vamvictor/Centinela-Nerf/Aplicacion/diana.png

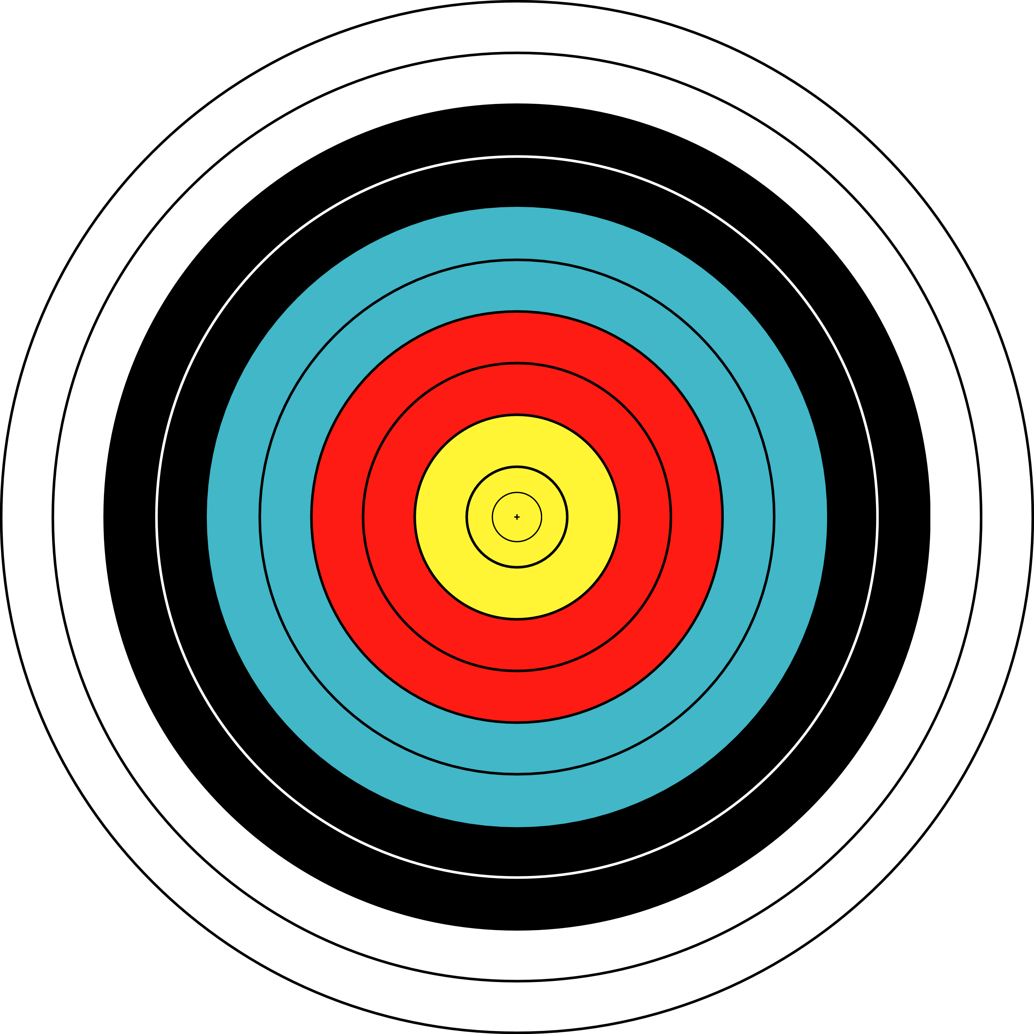
Aplicacion/diana.png
