vamvictor/Centinela-Nerf/Aplicacion/images/Bush/1.jpg

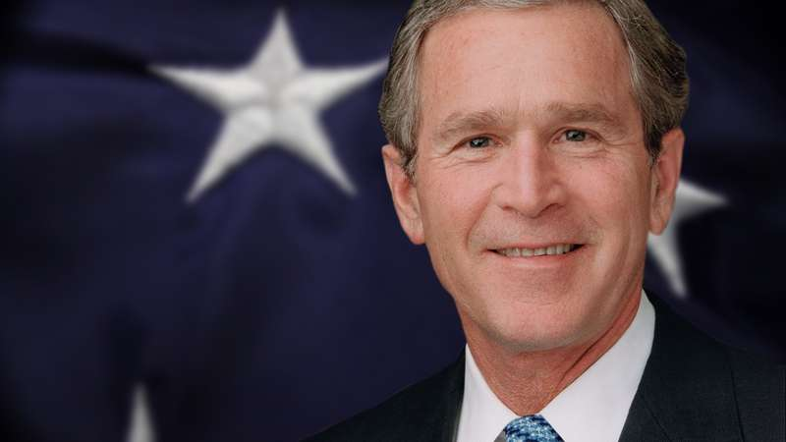
Aplicacion/images/Bush/1.jpg
