vamvictor/Centinela-Nerf/Aplicacion/images/Bush/2.jpg

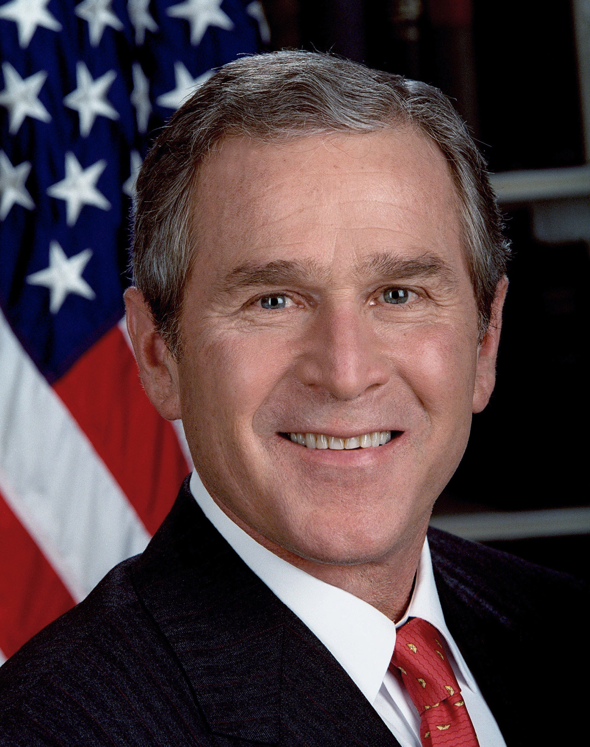
Aplicacion/images/Bush/2.jpg
