vamvictor/Centinela-Nerf/Aplicacion/images/Bush/3.jpg

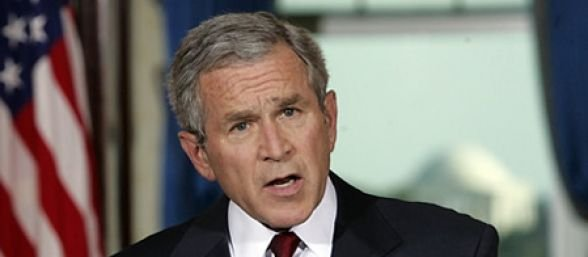
Aplicacion/images/Bush/3.jpg
