vamvictor/Centinela-Nerf/Aplicacion/images/Bush/4.jpg

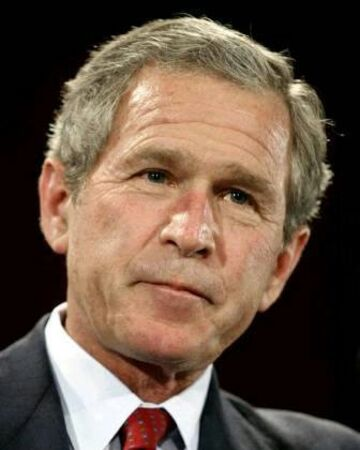
Aplicacion/images/Bush/4.jpg
