vamvictor/Centinela-Nerf/Aplicacion/images/Bush/5.jpg

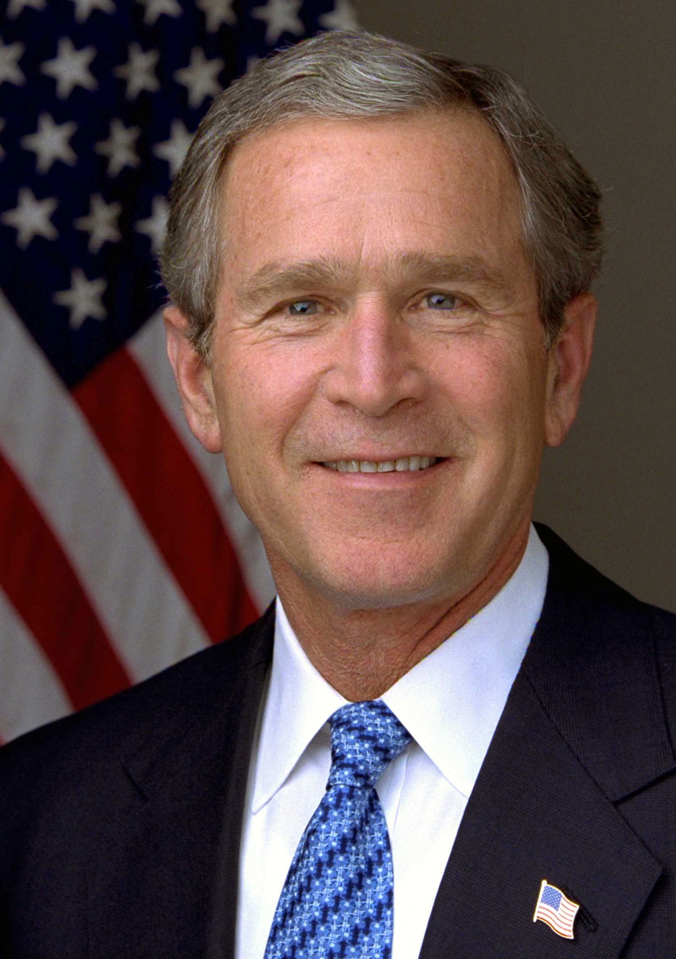
Aplicacion/images/Bush/5.jpg
