vamvictor/Centinela-Nerf/Aplicacion/images/Desconocidos/1.jpg

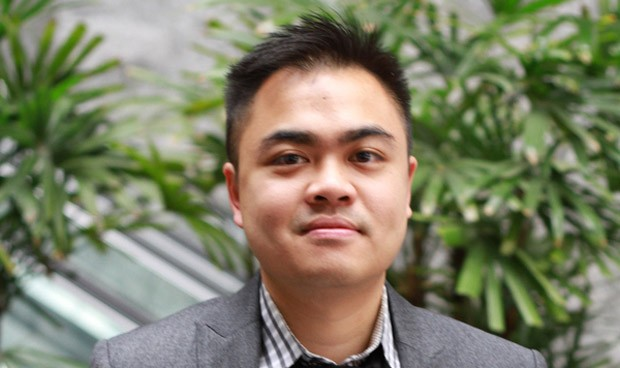
Aplicacion/images/Desconocidos/1.jpg
