vamvictor/Centinela-Nerf/Aplicacion/images/Desconocidos/2.png

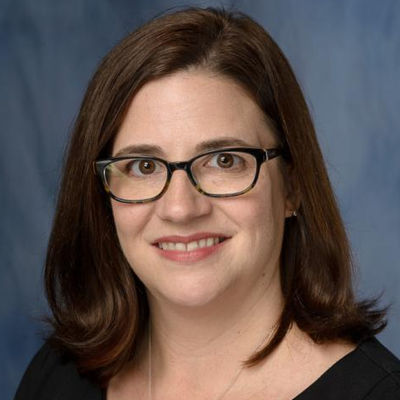
Aplicacion/images/Desconocidos/2.png
