vamvictor/Centinela-Nerf/Aplicacion/images/Desconocidos/3.jpg

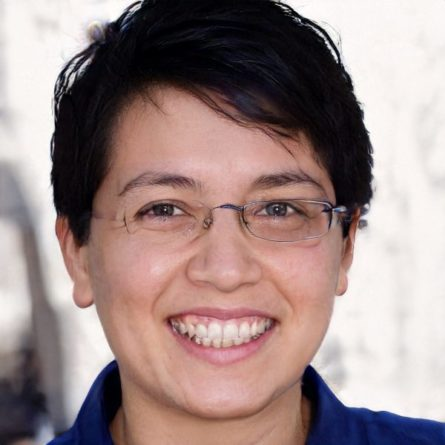
Aplicacion/images/Desconocidos/3.jpg
