vamvictor/Centinela-Nerf/Aplicacion/images/Desconocidos/4.jpg

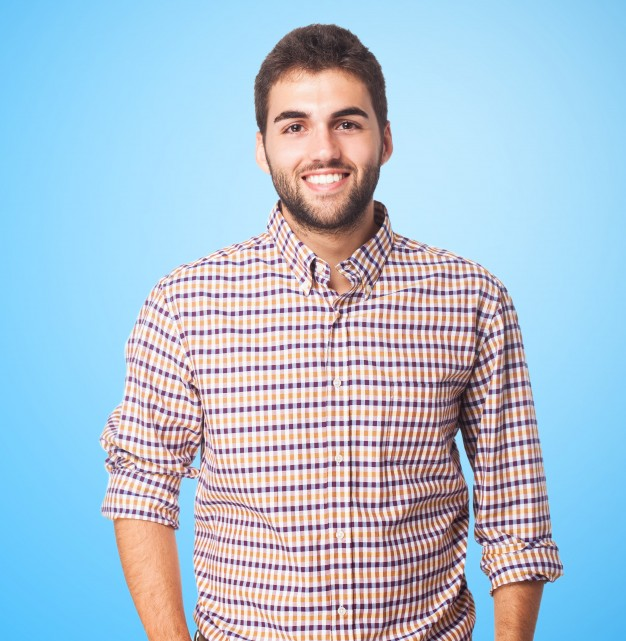
Aplicacion/images/Desconocidos/4.jpg
