vamvictor/Centinela-Nerf/Aplicacion/images/Desconocidos/5.jpg

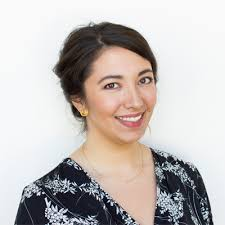
Aplicacion/images/Desconocidos/5.jpg
