vamvictor/Centinela-Nerf/Aplicacion/images/Desconocidos/6.jpg

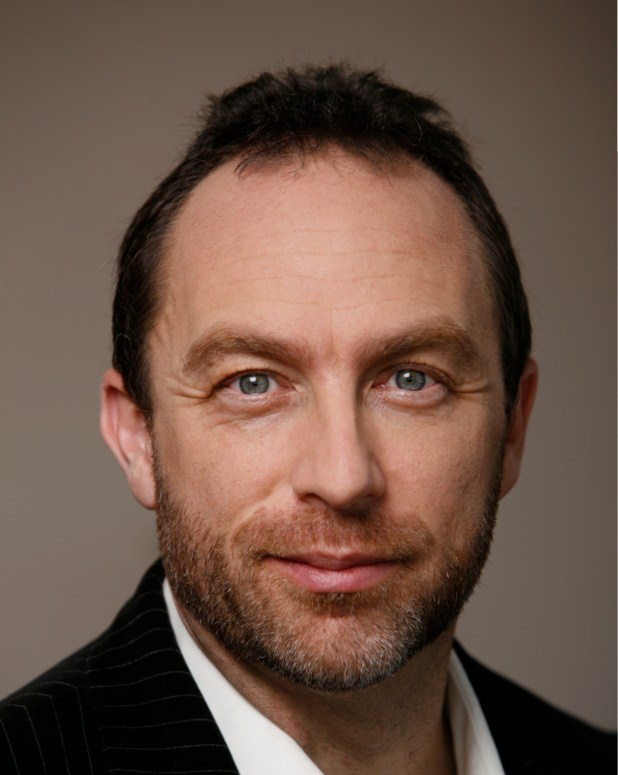
Aplicacion/images/Desconocidos/6.jpg
