vamvictor/Centinela-Nerf/Aplicacion/images/Desconocidos/7.jpg

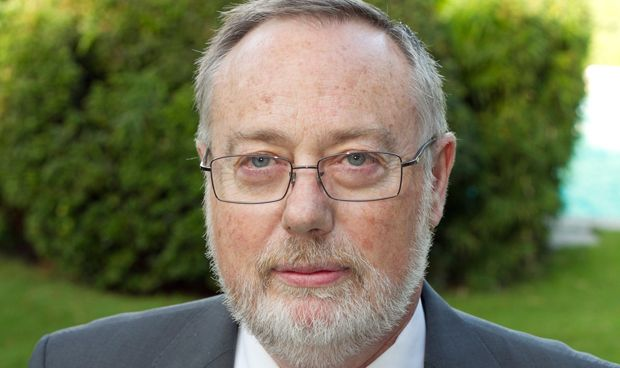
Aplicacion/images/Desconocidos/7.jpg
