vamvictor/Centinela-Nerf/Aplicacion/images/Desconocidos/8.jpg

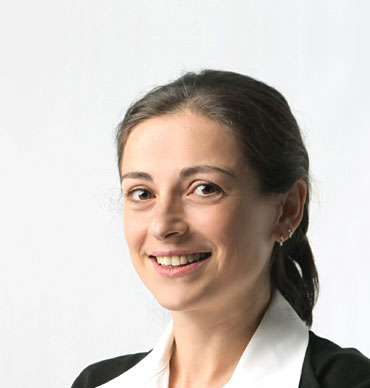
Aplicacion/images/Desconocidos/8.jpg
