vamvictor/Centinela-Nerf/Aplicacion/images/Kennedy/1.jpg

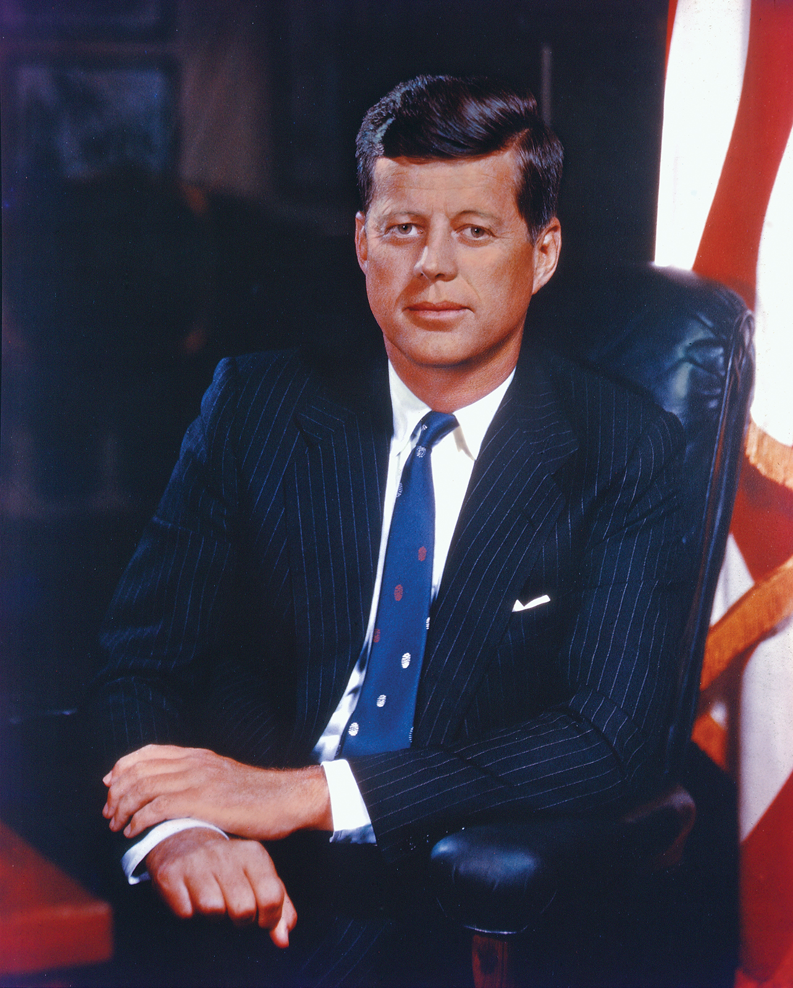
Aplicacion/images/Kennedy/1.jpg
