vamvictor/Centinela-Nerf/Aplicacion/images/Kennedy/2.jpg

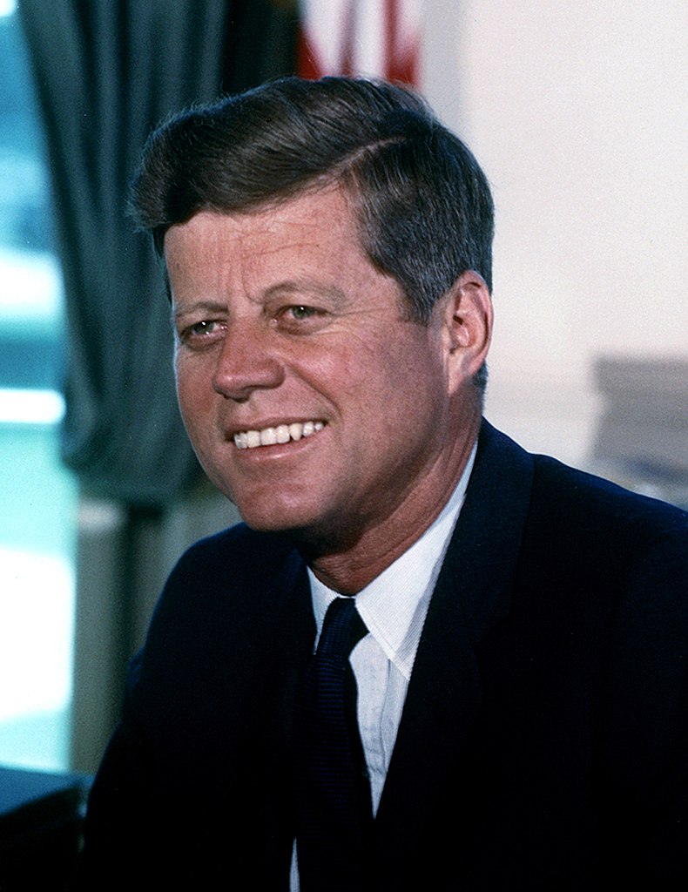
Aplicacion/images/Kennedy/2.jpg
