vamvictor/Centinela-Nerf/Aplicacion/images/Kennedy/3.jpg

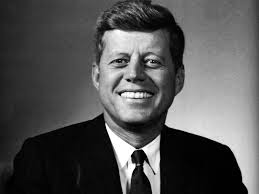
Aplicacion/images/Kennedy/3.jpg
