vamvictor/Centinela-Nerf/Aplicacion/images/Kennedy/4.jpg

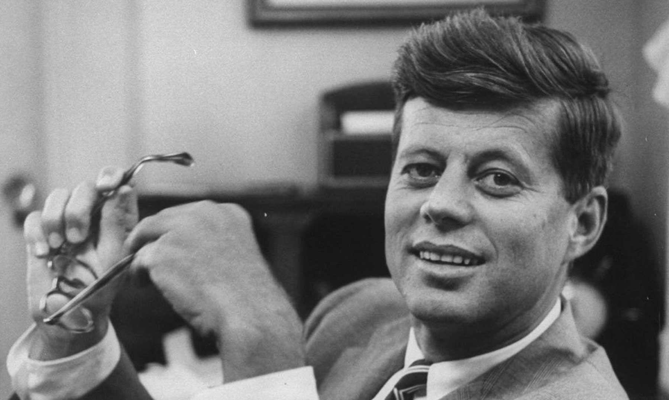
Aplicacion/images/Kennedy/4.jpg
