vamvictor/Centinela-Nerf/Aplicacion/images/Kennedy/5.jpg

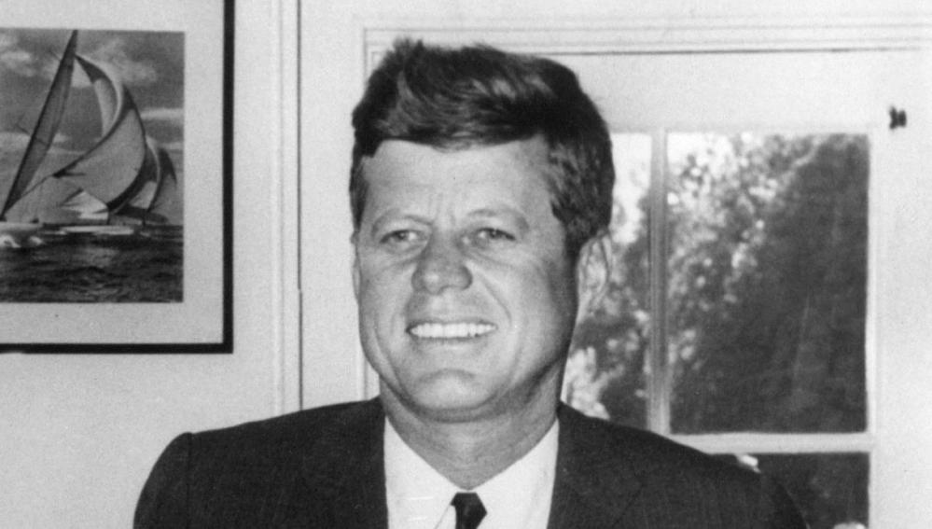
Aplicacion/images/Kennedy/5.jpg
