vamvictor/Centinela-Nerf/Aplicacion/images/Obama/1.jpg

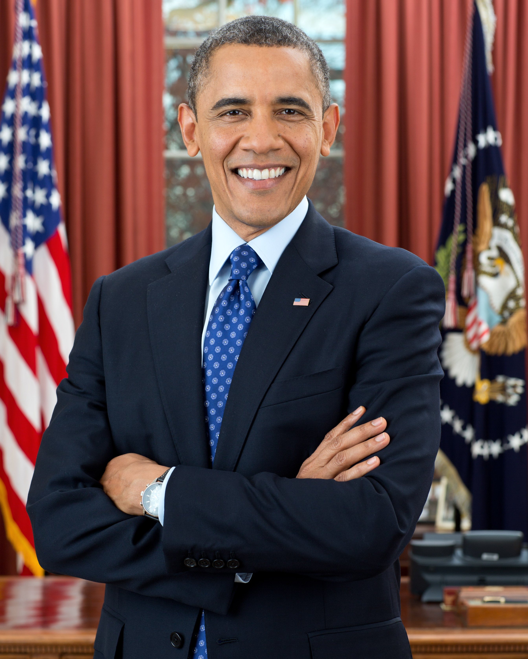
Aplicacion/images/Obama/1.jpg
