vamvictor/Centinela-Nerf/Aplicacion/images/Obama/2.jpg

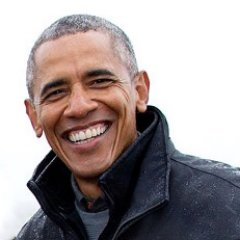
Aplicacion/images/Obama/2.jpg
