vamvictor/Centinela-Nerf/Aplicacion/images/Obama/3.jpg

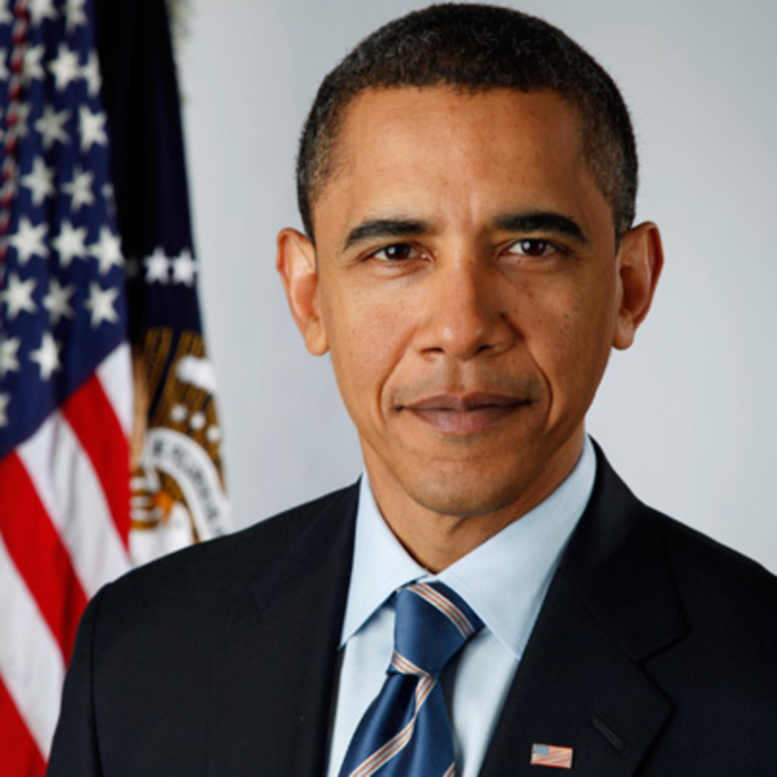
Aplicacion/images/Obama/3.jpg
