vamvictor/Centinela-Nerf/Aplicacion/images/Obama/4.jpg

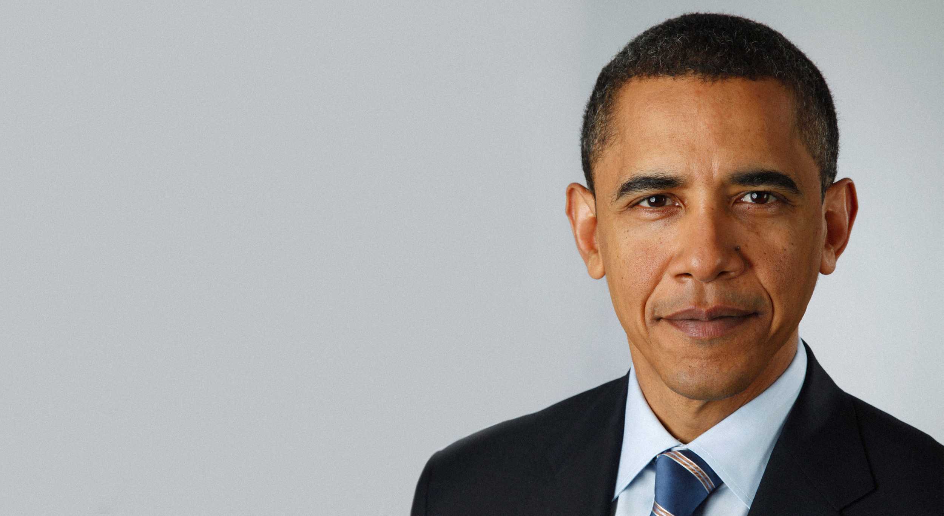
Aplicacion/images/Obama/4.jpg
