vamvictor/Centinela-Nerf/Aplicacion/images/Trump/1.jpg

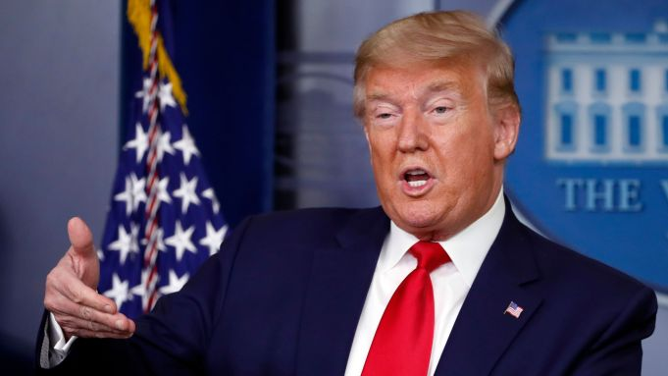
Aplicacion/images/Trump/1.jpg
