vamvictor/Centinela-Nerf/Aplicacion/images/Trump/2.jpg

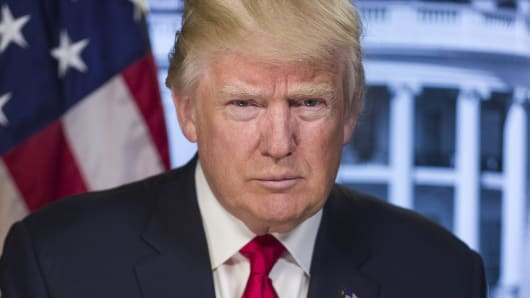
Aplicacion/images/Trump/2.jpg
