vamvictor/Centinela-Nerf/Aplicacion/images/Trump/3.jpg

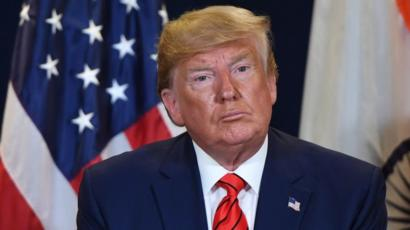
Aplicacion/images/Trump/3.jpg
