vamvictor/Centinela-Nerf/Aplicacion/images/Trump/5.jpg

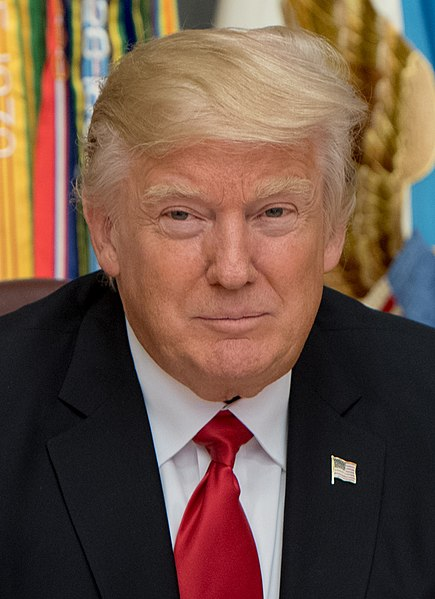
Aplicacion/images/Trump/5.jpg
