vamvictor/Centinela-Nerf/Aplicacion/images/Victor/1.jpg

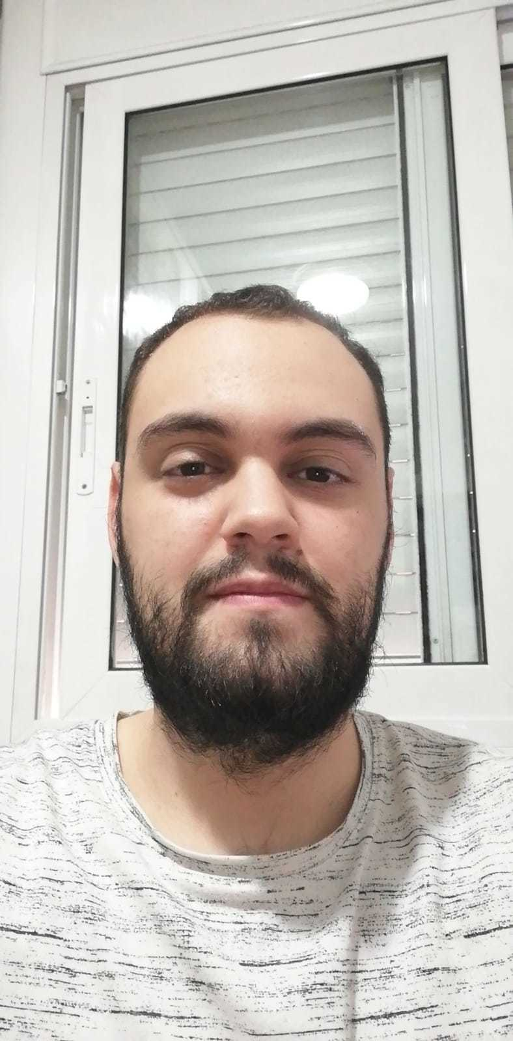
Aplicacion/images/Victor/1.jpg
