vamvictor/Centinela-Nerf/Aplicacion/images/Victor/2.jpg

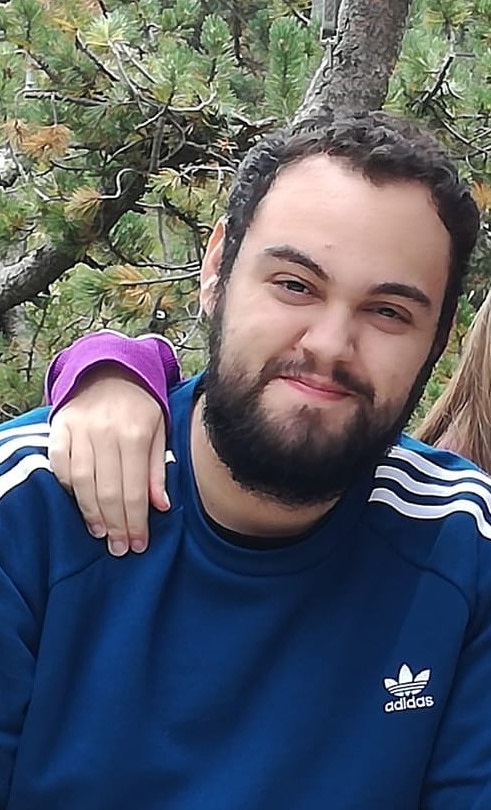
Aplicacion/images/Victor/2.jpg
