vamvictor/Centinela-Nerf/Aplicacion/images/Victor/3.jpg

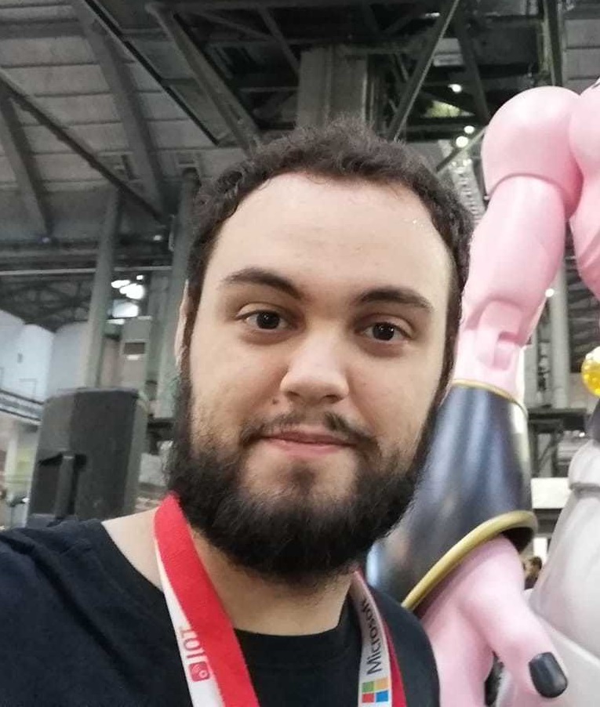
Aplicacion/images/Victor/3.jpg
