vamvictor/Centinela-Nerf/Aplicacion/images/Victor/4.jpg

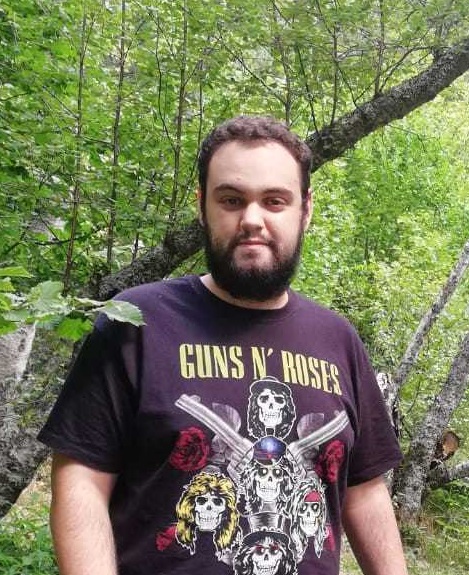
Aplicacion/images/Victor/4.jpg
