vamvictor/Centinela-Nerf/Aplicacion/images/Victor/5.jpg

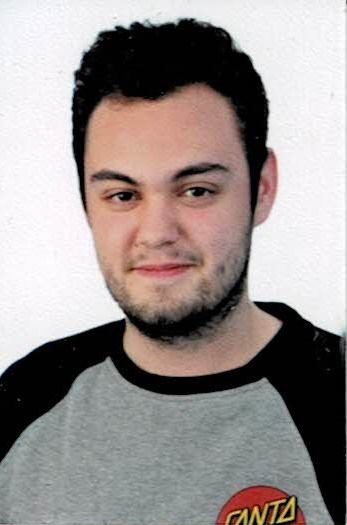
Aplicacion/images/Victor/5.jpg
