vamvictor/Centinela-Nerf/Aplicacion/images_mascarilla/Mascarilla/00001 (5).jpg

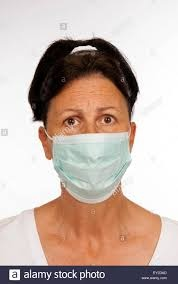
Aplicacion/images_mascarilla/Mascarilla/00001 (5).jpg
