vamvictor/Centinela-Nerf/Aplicacion/images_mascarilla/Mascarilla/00001 (17).jpg

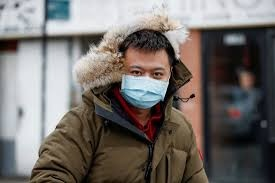
Aplicacion/images_mascarilla/Mascarilla/00001 (17).jpg
