vamvictor/Centinela-Nerf/Aplicacion/images_mascarilla/Mascarilla/2 (2).jpg

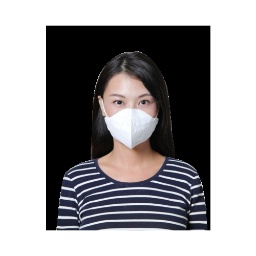
Aplicacion/images_mascarilla/Mascarilla/2 (2).jpg
