vamvictor/Centinela-Nerf/Aplicacion/images_mascarilla/Mascarilla/2 (4).jpg

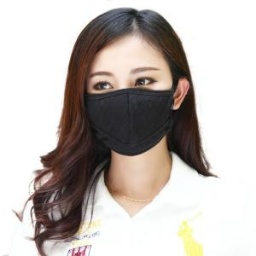
Aplicacion/images_mascarilla/Mascarilla/2 (4).jpg
