vamvictor/Centinela-Nerf/Aplicacion/images_mascarilla/Mascarilla/2 (5).jpg

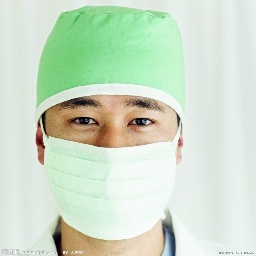
Aplicacion/images_mascarilla/Mascarilla/2 (5).jpg
