vamvictor/Centinela-Nerf/Aplicacion/images_mascarilla/Mascarilla/2 (7).jpg

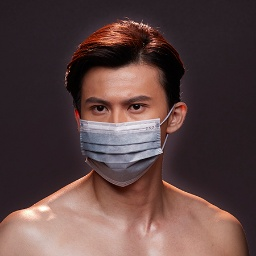
Aplicacion/images_mascarilla/Mascarilla/2 (7).jpg
