vamvictor/Centinela-Nerf/Aplicacion/images_mascarilla/Mascarilla/2 (12).jpg

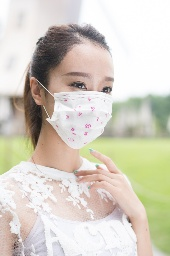
Aplicacion/images_mascarilla/Mascarilla/2 (12).jpg
