vamvictor/Centinela-Nerf/Aplicacion/images_mascarilla/Mascarilla/2 (13).jpg

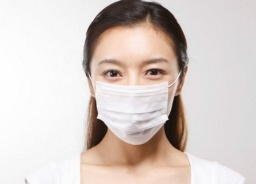
Aplicacion/images_mascarilla/Mascarilla/2 (13).jpg
