vamvictor/Centinela-Nerf/Aplicacion/images_mascarilla/Mascarilla/2 (14).jpg

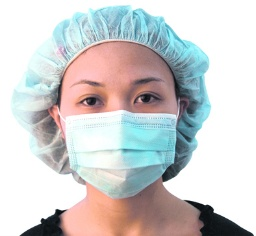
Aplicacion/images_mascarilla/Mascarilla/2 (14).jpg
