vamvictor/Centinela-Nerf/Aplicacion/images_mascarilla/Mascarilla/2 (16).jpg

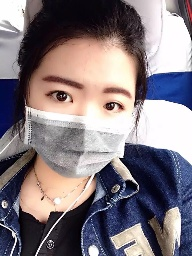
Aplicacion/images_mascarilla/Mascarilla/2 (16).jpg
