vamvictor/Centinela-Nerf/Aplicacion/images_mascarilla/Mascarilla/2 (24).jpg

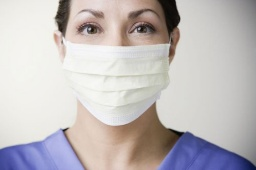
Aplicacion/images_mascarilla/Mascarilla/2 (24).jpg
