vamvictor/Centinela-Nerf/Aplicacion/images_mascarilla/Mascarilla/2 (25).jpg

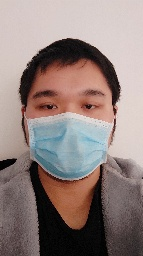
Aplicacion/images_mascarilla/Mascarilla/2 (25).jpg
