vamvictor/Centinela-Nerf/Aplicacion/images_mascarilla/Mascarilla/3 (6).jpg

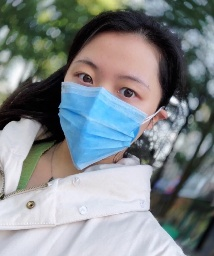
Aplicacion/images_mascarilla/Mascarilla/3 (6).jpg
