vamvictor/Centinela-Nerf/Aplicacion/images_mascarilla/Mascarilla/3 (7).jpg

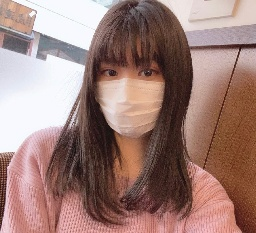
Aplicacion/images_mascarilla/Mascarilla/3 (7).jpg
