vamvictor/Centinela-Nerf/Aplicacion/images_mascarilla/Mascarilla/3 (9).jpg

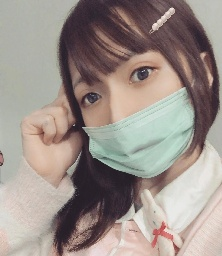
Aplicacion/images_mascarilla/Mascarilla/3 (9).jpg
