vamvictor/Centinela-Nerf/Aplicacion/images_mascarilla/Mascarilla/3 (11).jpg

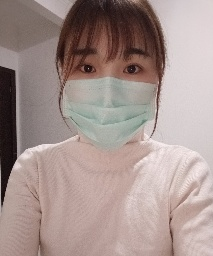
Aplicacion/images_mascarilla/Mascarilla/3 (11).jpg
