vamvictor/Centinela-Nerf/Aplicacion/images_mascarilla/Mascarilla/3 (16).jpg

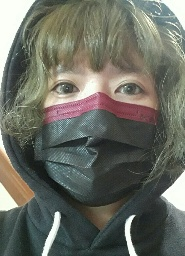
Aplicacion/images_mascarilla/Mascarilla/3 (16).jpg
