vamvictor/Centinela-Nerf/Aplicacion/images_mascarilla/Mascarilla/0003.jpg

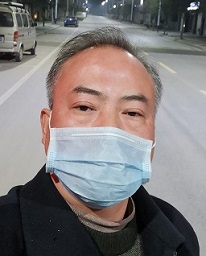
Aplicacion/images_mascarilla/Mascarilla/0003.jpg
