vamvictor/Centinela-Nerf/Aplicacion/images_mascarilla/Mascarilla/5 (92).jpg

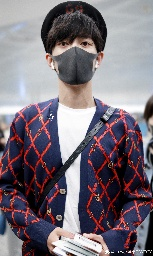
Aplicacion/images_mascarilla/Mascarilla/5 (92).jpg
