vamvictor/Centinela-Nerf/Aplicacion/images_mascarilla/Mascarilla/0015.jpg

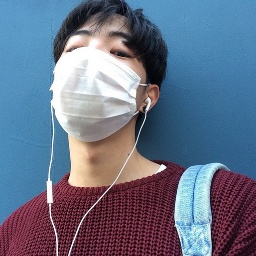
Aplicacion/images_mascarilla/Mascarilla/0015.jpg
