vamvictor/Centinela-Nerf/Aplicacion/images_mascarilla/Mascarilla/0020.jpg

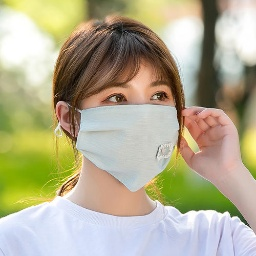
Aplicacion/images_mascarilla/Mascarilla/0020.jpg
