vamvictor/Centinela-Nerf/Aplicacion/images_mascarilla/Mascarilla/00031 (6).jpg

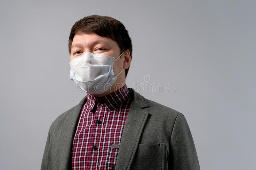
Aplicacion/images_mascarilla/Mascarilla/00031 (6).jpg
