vamvictor/Centinela-Nerf/Aplicacion/images_mascarilla/Mascarilla/00031 (29).jpg

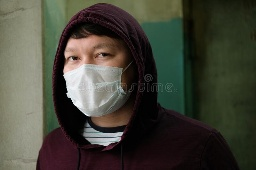
Aplicacion/images_mascarilla/Mascarilla/00031 (29).jpg
