vamvictor/Centinela-Nerf/Aplicacion/images_mascarilla/Mascarilla/00031 (82).jpg

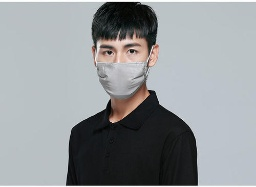
Aplicacion/images_mascarilla/Mascarilla/00031 (82).jpg
