vamvictor/Centinela-Nerf/Aplicacion/images_mascarilla/Mascarilla/00031 (93).jpg

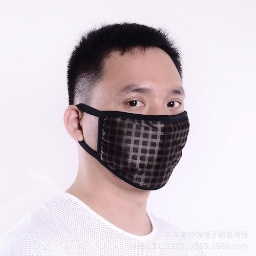
Aplicacion/images_mascarilla/Mascarilla/00031 (93).jpg
