vamvictor/Centinela-Nerf/Aplicacion/images_mascarilla/Mascarilla/0036.jpg

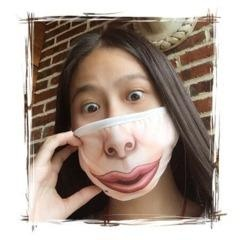
Aplicacion/images_mascarilla/Mascarilla/0036.jpg
