vamvictor/Centinela-Nerf/Aplicacion/images_mascarilla/Mascarilla/0056.jpg

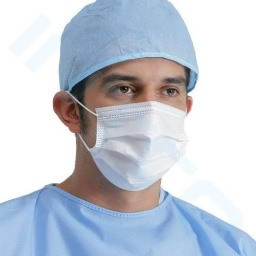
Aplicacion/images_mascarilla/Mascarilla/0056.jpg
