vamvictor/Centinela-Nerf/Aplicacion/images_mascarilla/Mascarilla/0065.jpg

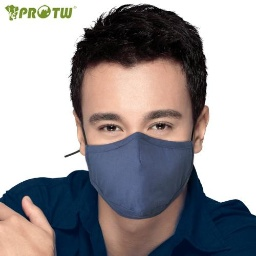
Aplicacion/images_mascarilla/Mascarilla/0065.jpg
