vamvictor/Centinela-Nerf/Aplicacion/images_mascarilla/Mascarilla/0067.jpg

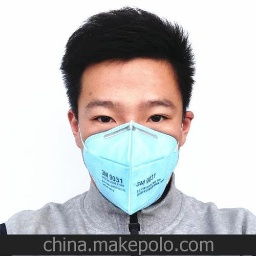
Aplicacion/images_mascarilla/Mascarilla/0067.jpg
