vamvictor/Centinela-Nerf/Aplicacion/images_mascarilla/Mascarilla/0093.jpg

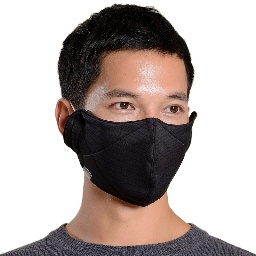
Aplicacion/images_mascarilla/Mascarilla/0093.jpg
