vamvictor/Centinela-Nerf/Aplicacion/images_mascarilla/Mascarilla/0111.jpg

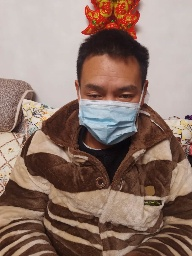
Aplicacion/images_mascarilla/Mascarilla/0111.jpg
