vamvictor/Centinela-Nerf/Aplicacion/images_mascarilla/Mascarilla/0127.jpg

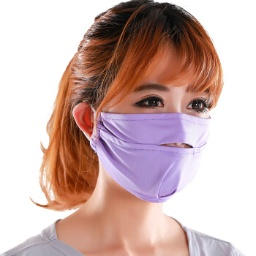
Aplicacion/images_mascarilla/Mascarilla/0127.jpg
