vamvictor/Centinela-Nerf/Aplicacion/images_mascarilla/Mascarilla/0140.jpg

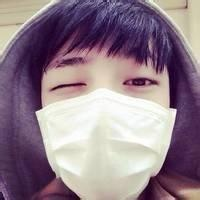
Aplicacion/images_mascarilla/Mascarilla/0140.jpg
