vamvictor/Centinela-Nerf/Aplicacion/images_mascarilla/Mascarilla/0156.jpg

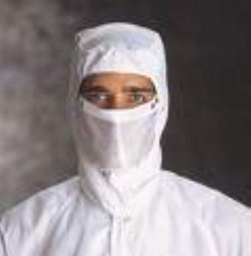
Aplicacion/images_mascarilla/Mascarilla/0156.jpg
