vamvictor/Centinela-Nerf/Aplicacion/images_mascarilla/Mascarilla/0171.jpg

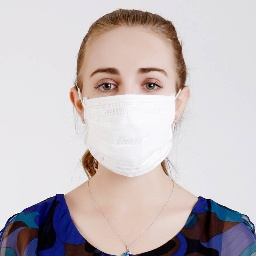
Aplicacion/images_mascarilla/Mascarilla/0171.jpg
