vamvictor/Centinela-Nerf/Aplicacion/images_mascarilla/Mascarilla/0180.jpg

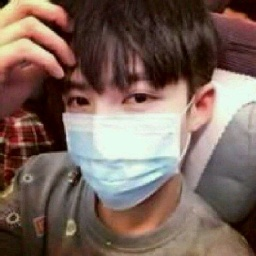
Aplicacion/images_mascarilla/Mascarilla/0180.jpg
