vamvictor/Centinela-Nerf/Aplicacion/images_mascarilla/Mascarilla/0220.jpg

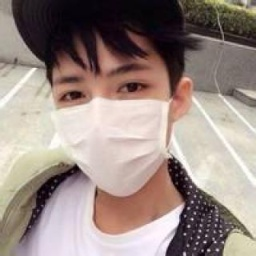
Aplicacion/images_mascarilla/Mascarilla/0220.jpg
