vamvictor/Centinela-Nerf/Aplicacion/images_mascarilla/Mascarilla/0222.jpg

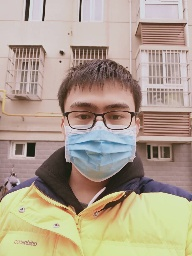
Aplicacion/images_mascarilla/Mascarilla/0222.jpg
