vamvictor/Centinela-Nerf/Aplicacion/images_mascarilla/Mascarilla/0231.jpg

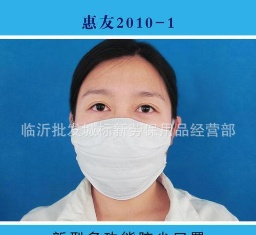
Aplicacion/images_mascarilla/Mascarilla/0231.jpg
