vamvictor/Centinela-Nerf/Aplicacion/images_mascarilla/Mascarilla/0235.jpg

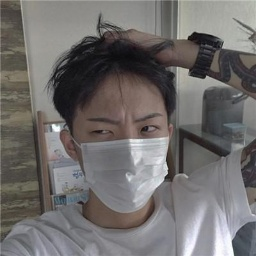
Aplicacion/images_mascarilla/Mascarilla/0235.jpg
