vamvictor/Centinela-Nerf/Aplicacion/images_mascarilla/Mascarilla/0260.jpg

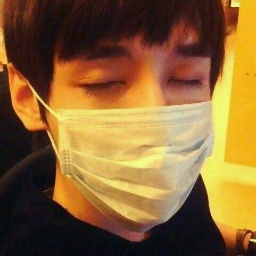
Aplicacion/images_mascarilla/Mascarilla/0260.jpg
