vamvictor/Centinela-Nerf/Aplicacion/images_mascarilla/Mascarilla/0266.jpg

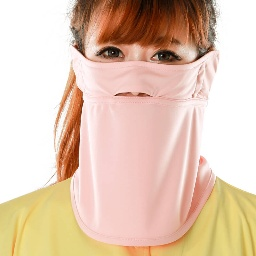
Aplicacion/images_mascarilla/Mascarilla/0266.jpg
