vamvictor/Centinela-Nerf/Aplicacion/images_mascarilla/Mascarilla/0267.jpg

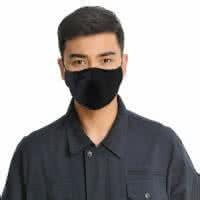
Aplicacion/images_mascarilla/Mascarilla/0267.jpg
