vamvictor/Centinela-Nerf/Aplicacion/images_mascarilla/Mascarilla/0271.jpg

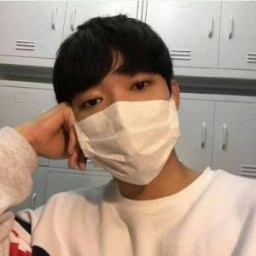
Aplicacion/images_mascarilla/Mascarilla/0271.jpg
