vamvictor/Centinela-Nerf/Aplicacion/images_mascarilla/Mascarilla/0277.jpg

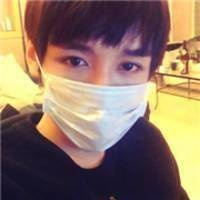
Aplicacion/images_mascarilla/Mascarilla/0277.jpg
