vamvictor/Centinela-Nerf/Aplicacion/images_mascarilla/Mascarilla/0299.jpg

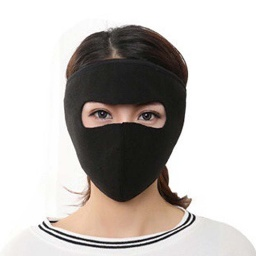
Aplicacion/images_mascarilla/Mascarilla/0299.jpg
