vamvictor/Centinela-Nerf/Aplicacion/images_mascarilla/No_Mascarilla/4356490-celebrar-mujer-cruzó-en-ambas-manos-para-poner-fin-a-su-boca-para-hablar-aislado-en-el-fo.jpg

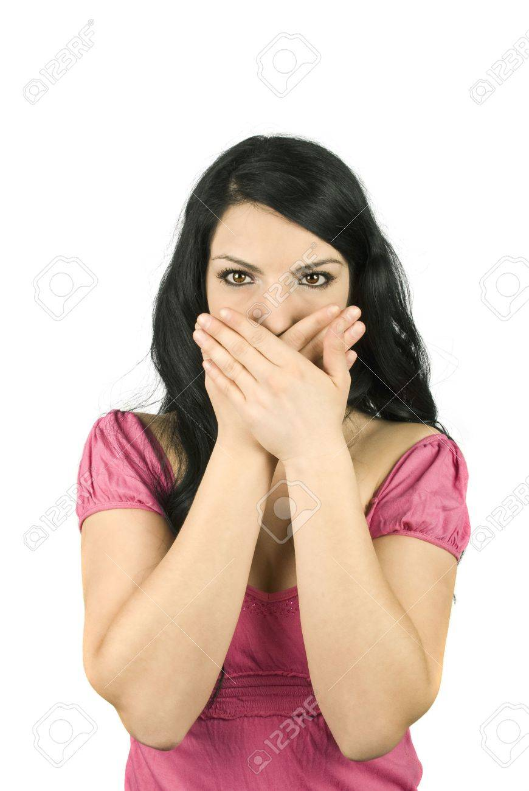
Aplicacion/images_mascarilla/No_Mascarilla/4356490-celebrar-mujer-cruzó-en-ambas-manos-para-poner-fin-a-su-boca-para-hablar-aislado-en-el-fo.jpg
