vamvictor/Centinela-Nerf/Aplicacion/images_mascarilla/No_Mascarilla/37323125-mujer-tapándose-la-cara-con-las-dos-manos-aisladas-en-un-fondo-blanco.jpg

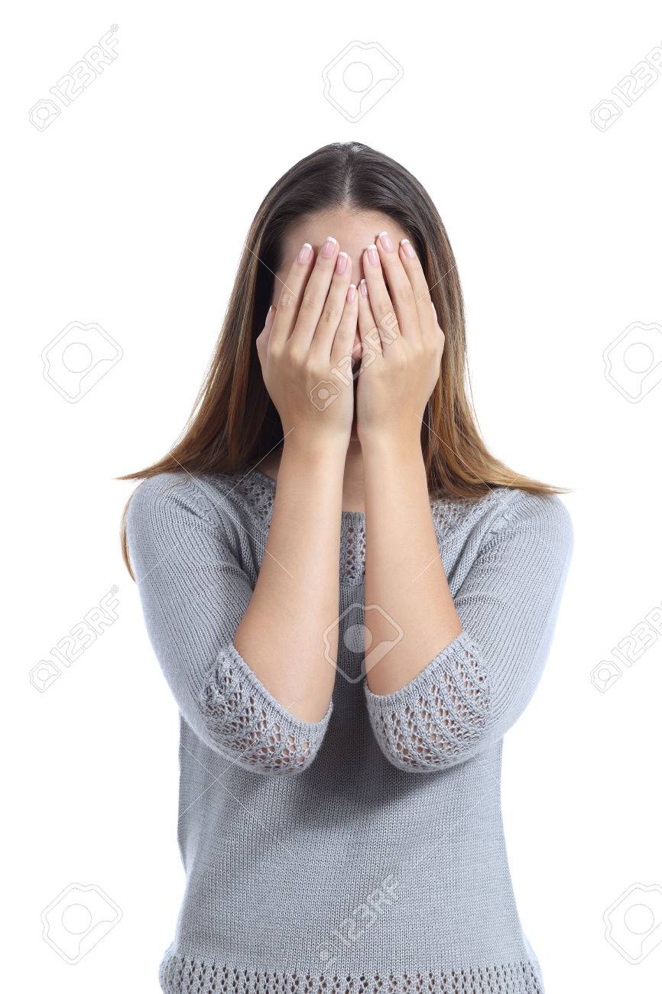
Aplicacion/images_mascarilla/No_Mascarilla/37323125-mujer-tapándose-la-cara-con-las-dos-manos-aisladas-en-un-fondo-blanco.jpg
