vamvictor/Centinela-Nerf/Aplicacion/images_mascarilla/No_Mascarilla/capturadepantalla20180405alas30029pm-18358e458a35a8448e3aafab6e91edb7-1200x800.jpg

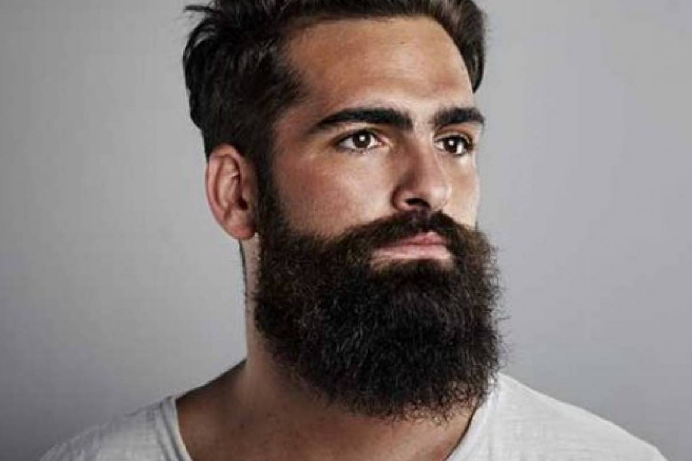
Aplicacion/images_mascarilla/No_Mascarilla/capturadepantalla20180405alas30029pm-18358e458a35a8448e3aafab6e91edb7-1200x800.jpg
