vamvictor/Centinela-Nerf/Aplicacion/images_mascarilla/No_Mascarilla/cara-con-las-manos-cara-de-ocultación-de-la-cubierta-de-la-muchacha-con-las-manos-45298858.jpg

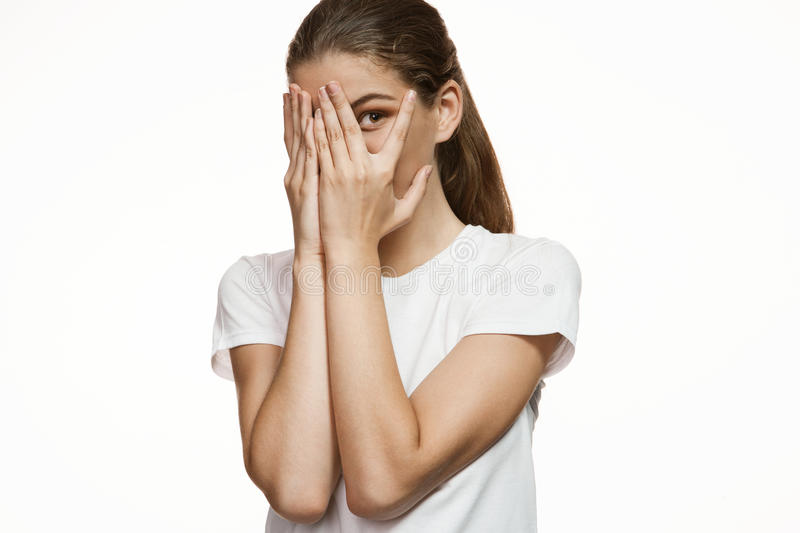
Aplicacion/images_mascarilla/No_Mascarilla/cara-con-las-manos-cara-de-ocultación-de-la-cubierta-de-la-muchacha-con-las-manos-45298858.jpg
