vamvictor/Centinela-Nerf/Aplicacion/images_mascarilla/No_Mascarilla/cortó-barba.jpg

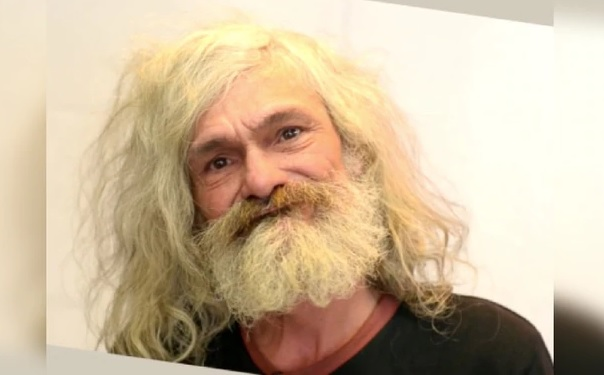
Aplicacion/images_mascarilla/No_Mascarilla/cortó-barba.jpg
