vamvictor/Centinela-Nerf/Aplicacion/images_mascarilla/No_Mascarilla/estornudar--644x483.jpg

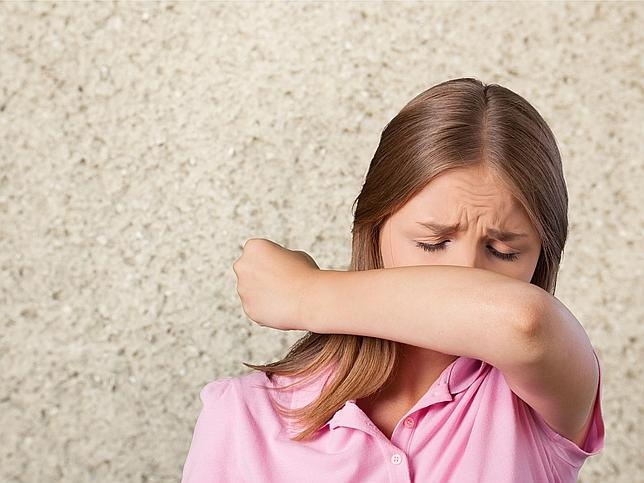
Aplicacion/images_mascarilla/No_Mascarilla/estornudar--644x483.jpg
