vamvictor/Centinela-Nerf/Aplicacion/images_mascarilla/No_Mascarilla/featuredImage-19718-es-oficial-los-hombres-con-barba-son-los-mas-atractivos-992x558@LaVanguardia-.jpg

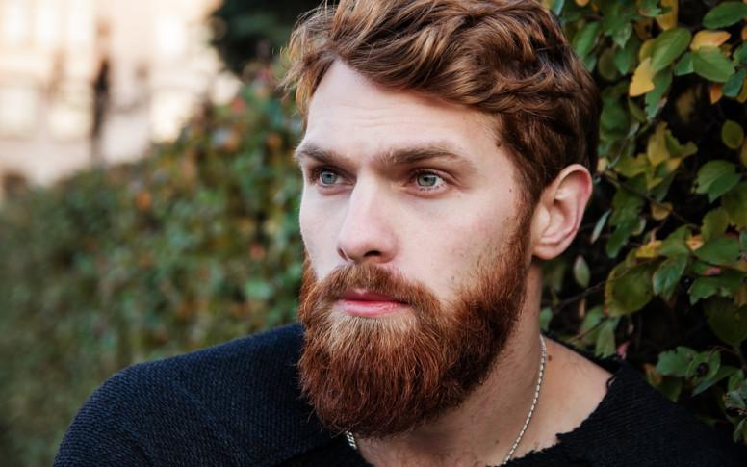
Aplicacion/images_mascarilla/No_Mascarilla/featuredImage-19718-es-oficial-los-hombres-con-barba-son-los-mas-atractivos-992x558@LaVanguardia-.jpg
