vamvictor/Centinela-Nerf/Aplicacion/images_mascarilla/No_Mascarilla/Hombre-barba-41-1024x768.jpg

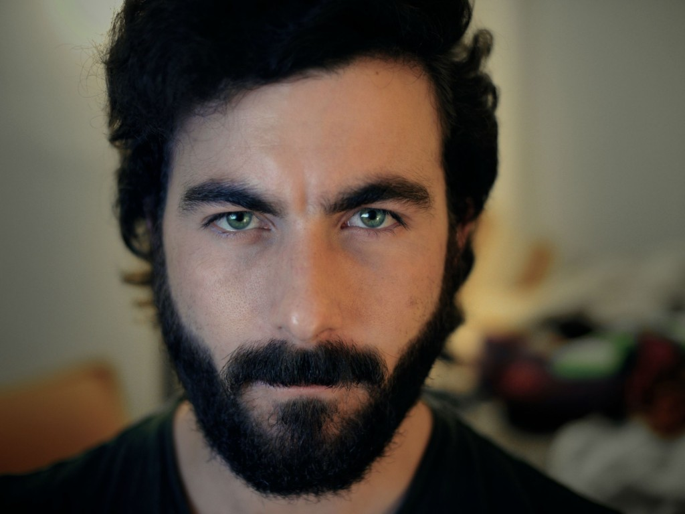
Aplicacion/images_mascarilla/No_Mascarilla/Hombre-barba-41-1024x768.jpg
