vamvictor/Centinela-Nerf/Aplicacion/images_mascarilla/No_Mascarilla/hombre-barba_1303-9367.jpg

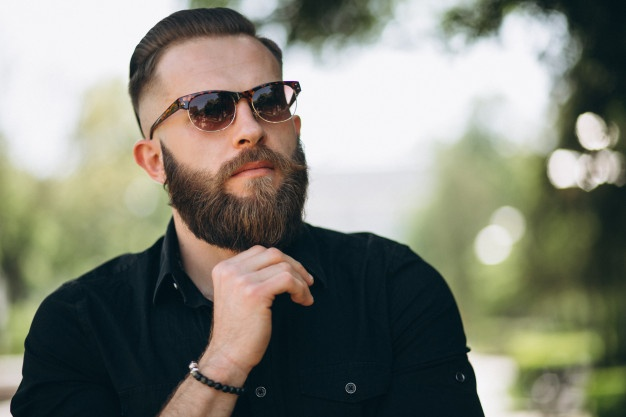
Aplicacion/images_mascarilla/No_Mascarilla/hombre-barba_1303-9367.jpg
