vamvictor/Centinela-Nerf/Aplicacion/images_mascarilla/No_Mascarilla/hombre-manos-cara-asustada_70560-48.jpg

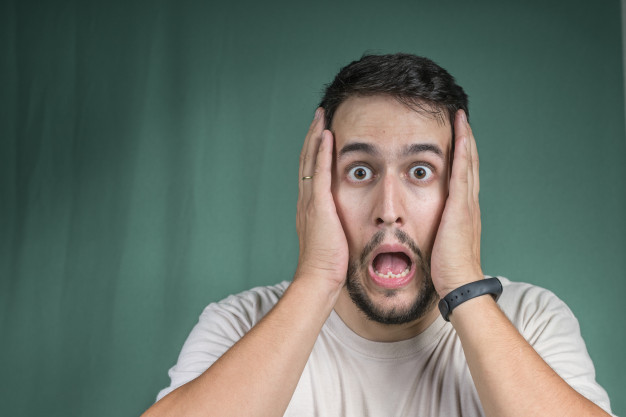
Aplicacion/images_mascarilla/No_Mascarilla/hombre-manos-cara-asustada_70560-48.jpg
