vamvictor/Centinela-Nerf/Piezas 3D/robot simulacion.png

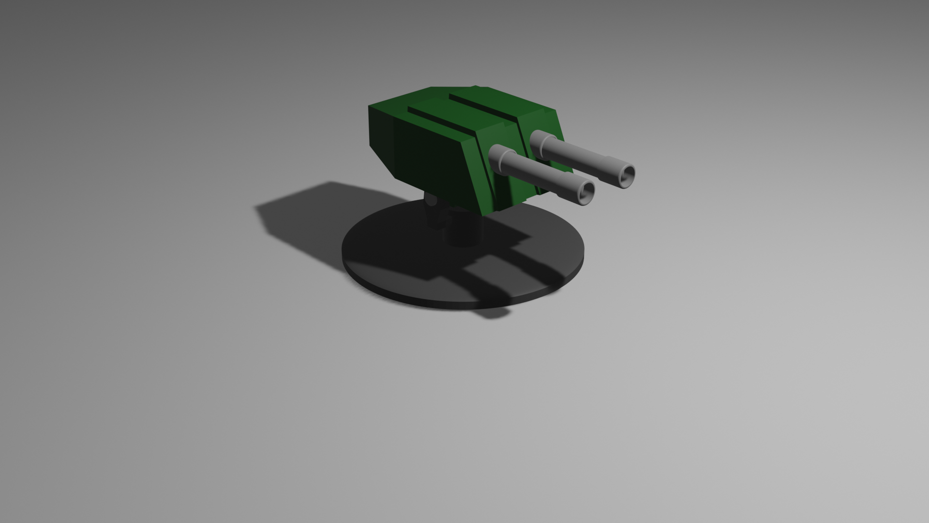
Piezas 3D/robot simulacion.png
