vamvictor/Centinela-Nerf/Piezas 3D/robot-impresion.png

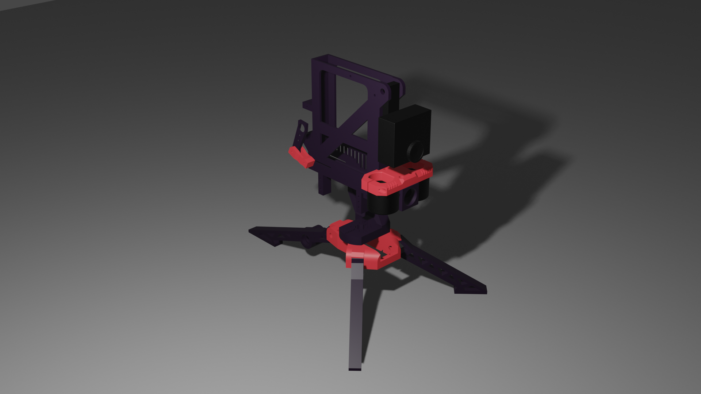
Piezas 3D/robot-impresion.png
