vamvictor/Centinela-Nerf/Piezas 3D/3d Parts Real/Tilt_bracket_bottom.stl

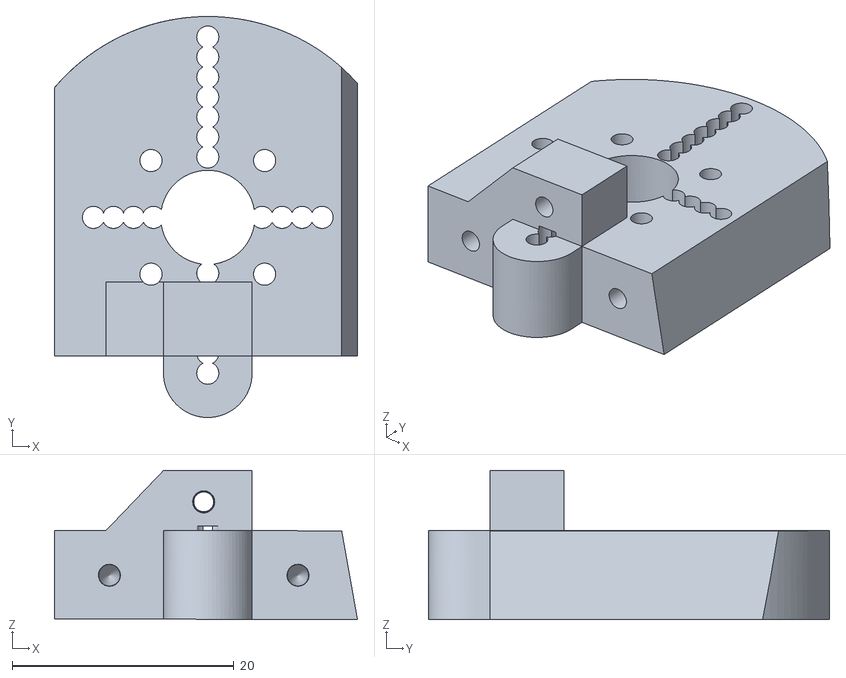
[picture p135: CAD file, 2020-05-26]
Piezas 3D/3d Parts Real/Tilt_bracket_bottom.stl
27.3 x 36.2 x 13.5
