vamvictor/Centinela-Nerf/Piezas 3D/3d Parts Real/long_leg_cap_round.stl

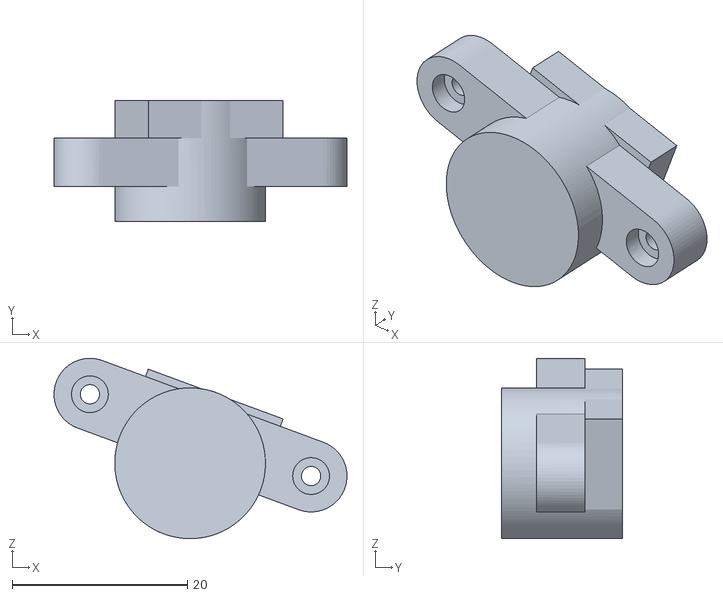
[picture p136: CAD file, 2020-05-26]
Piezas 3D/3d Parts Real/long_leg_cap_round.stl
33.4 x 13.8 x 20.6
